TITAN-2/2324_projet2A_drone_SousMarin/Stm32/RECEPTION_UART_H7A3ZIQ/Core/Src/Process.c

/*
 * Process.c
 *
 *  Created on: Jan 17, 2024
 *      Author: romingo
 */

#include "Process.h"

void Thrust_Init(void){

	HAL_TIM_PWM_Start(TIM_PROP_G.TIM, TIM_PROP_G.CHANNEL);
	HAL_Delay(500);
	__HAL_TIM_SET_COMPARE(TIM_PROP_G.TIM, TIM_PROP_G.CHANNEL, MIN_Thrust);
	HAL_Delay(500);
	__HAL_TIM_SET_COMPARE(TIM_PROP_G.TIM, TIM_PROP_G.CHANNEL, MAX_Thrust);
	HAL_Delay(500);
	__HAL_TIM_SET_COMPARE(TIM_PROP_G.TIM, TIM_PROP_G.CHANNEL, MIN_Thrust);
	HAL_Delay(500);
	HAL_TIM_PWM_Start(TIM_PROP_D.TIM, TIM_PROP_D.CHANNEL);
	HAL_Delay(500);

	__HAL_TIM_SET_COMPARE(TIM_PROP_D.TIM, TIM_PROP_D.CHANNEL, MIN_Thrust);

	HAL_Delay(500);
	__HAL_TIM_SET_COMPARE(TIM_PROP_D.TIM, TIM_PROP_D.CHANNEL, MAX_Thrust);
	HAL_Delay(500);
	__HAL_TIM_SET_COMPARE(TIM_PROP_D.TIM, TIM_PROP_D.CHANNEL, MIN_Thrust);
	HAL_Delay(500);

}
void Depth_Init(void){
	uint8_t t=0;
	while(t<100){
		//XL320_set_led_ON(XL_Front.huartXL,2); //Green Led
		XL320_set_led_ON(XL_Back.huartXL,2);
		XL320_set_torque_enable(XL_Back.huartXL);
		XL320_set_pos(XL_Front.huartXL, ( uint16_t )0);
		XL320_set_pos(XL_Back.huartXL, ( uint16_t )0);
		t++;
	}

}
void Process_Init(void){
	Thrust_Init();
	Depth_Init();
}

void Process(receiveMsg* message) {
    AdjustAngle(message->thrust,message->angle);
    AdjustDepth(&XL_Net,message->depth);
}

void AdjustThrust( TIM_PROP* tim_prop, uint8_t thrust) {
	float thrust_ms = 1-(thrust * ((float)(MIN_Thrust - MAX_Thrust) / 100.0)) + MIN_Thrust;
    __HAL_TIM_SET_COMPARE(tim_prop->TIM, tim_prop->CHANNEL,thrust_ms);
}

void AdjustAngle(uint8_t thrust,int8_t angle){
	uint8_t thrust_G = thrust;
	uint8_t thrust_D = thrust;

	if (angle<50){//On tourne a gauche
		thrust_G = thrust;
		thrust_D = 0; // Ajouter une diminution progressive des pousses moteurs
	}
	if (angle>50){//On tourne a droite
		thrust_G = 0;
		thrust_D = thrust;
	}
	AdjustThrust(&TIM_PROP_G, thrust_G);
	AdjustThrust(&TIM_PROP_D, thrust_D);
}

void AdjustDepth(XL_Network* XL_Net,uint8_t depth){
	//Logique:
	//on repartit équitablement la descente des ballasts

	//XL320_set_pos(XL_Net->XL_Front->huartXL , depth*3); // Dans XL320_set_pos on map de 0,300 --> 0,1023 ici on veut map de 0,100 --> 0,1023
	XL320_set_pos(XL_Net->XL_Back->huartXL , (uint16_t)depth*3);
	XL320_set_led_ON(XL_Net->XL_Back->huartXL , 5);

	XL_Net->XL_Front->pos = (uint16_t)depth*3;
	XL_Net->XL_Back->pos = (uint16_t)depth*3;


}
